SafeHazard/Clip-Boy/Clip-Boy/images/Clip Boy Final - NV 153x192.png

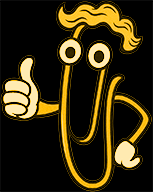
Clip-Boy/images/Clip Boy Final - NV 153x192.png
