SafeHazard/Clip-Boy/Clip-Boy/shots/signal_loss/aplist_01_target_present.bmp

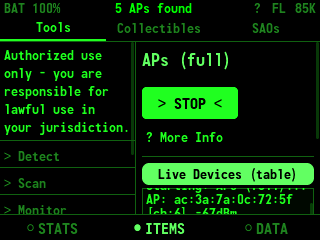
Clip-Boy/shots/signal_loss/aplist_01_target_present.bmp
