SafeHazard/Clip-Boy/Clip-Boy/shots/signal_loss/ble_01_advertiser_up.bmp

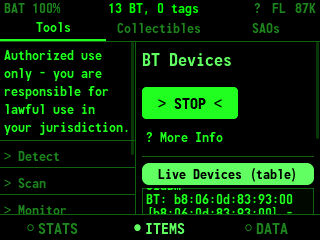
Clip-Boy/shots/signal_loss/ble_01_advertiser_up.bmp
