SafeHazard/Clip-Boy/Clip-Boy/shots/signal_loss/rssi_02_noselect.bmp

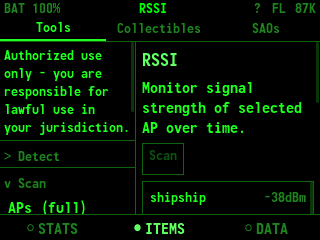
Clip-Boy/shots/signal_loss/rssi_02_noselect.bmp
