SafeHazard/Clip-Boy/Clip-Boy/shots/signal_loss/rssi_03_selected.bmp

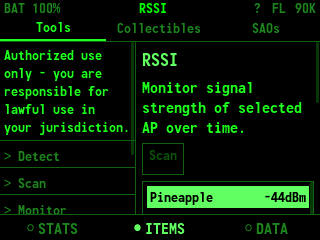
Clip-Boy/shots/signal_loss/rssi_03_selected.bmp
