SafeHazard/Clip-Boy/Clip-Boy/web_images/1.png

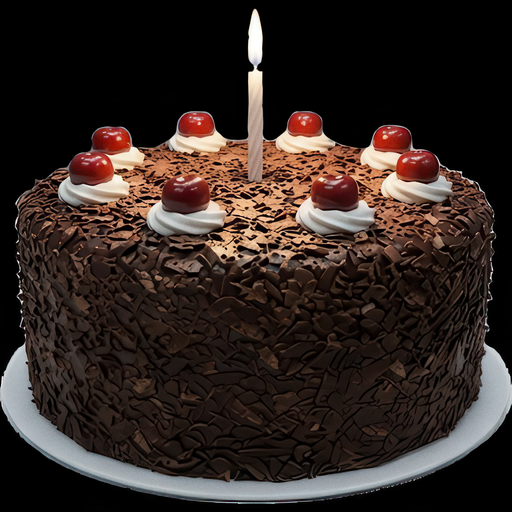
Clip-Boy/web_images/1.png
