SafeHazard/Clip-Boy/Clip-Boy/web_images/2.png

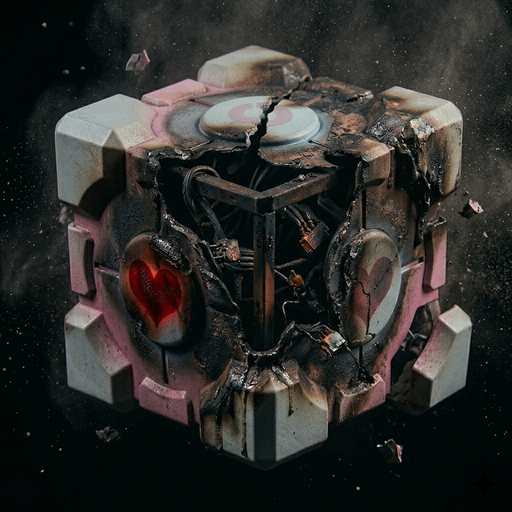
Clip-Boy/web_images/2.png
