SafeHazard/Clip-Boy/Clip-Boy/web_images/3.png

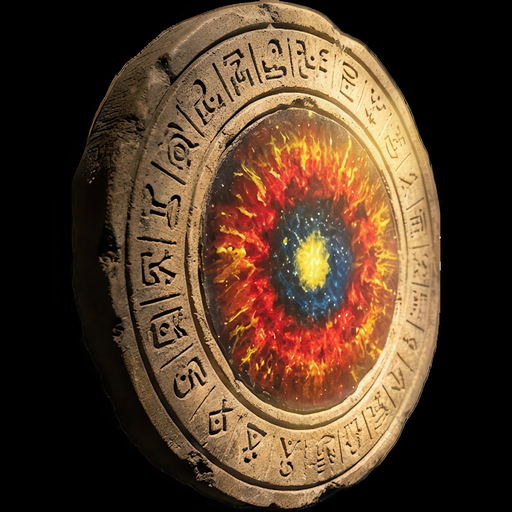
Clip-Boy/web_images/3.png
