SafeHazard/Clip-Boy/Clip-Boy/web_images/4.png

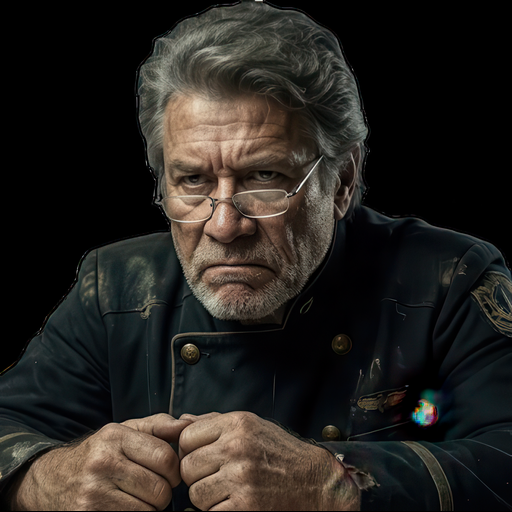
Clip-Boy/web_images/4.png
