SafeHazard/Clip-Boy/Clip-Boy/web_images/5.png

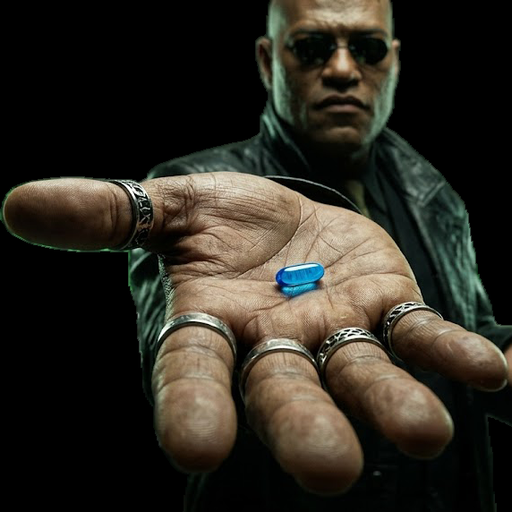
Clip-Boy/web_images/5.png
