SafeHazard/Clip-Boy/Clip-Boy/web_images/6.png

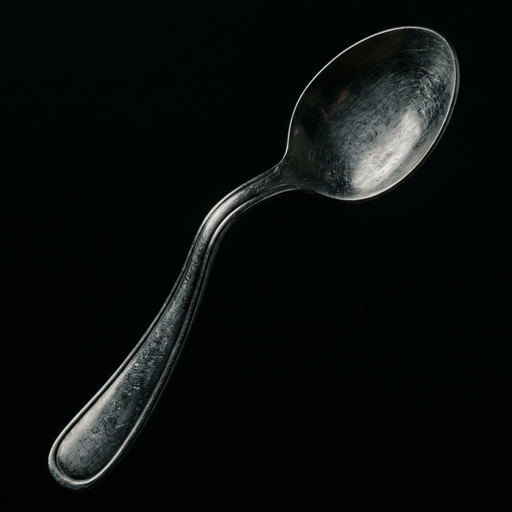
Clip-Boy/web_images/6.png
