SafeHazard/Clip-Boy/Clip-Boy/web_images/7.png

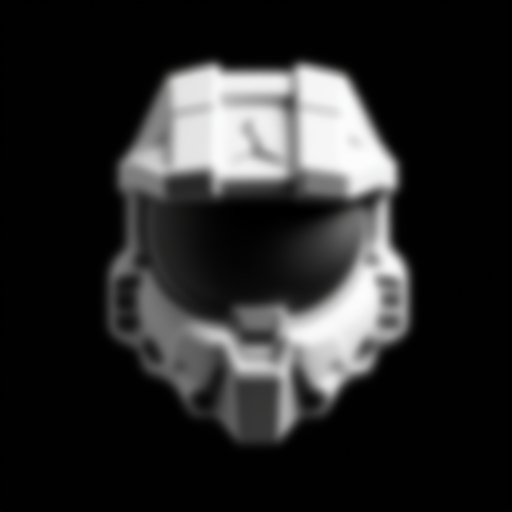
Clip-Boy/web_images/7.png
