SafeHazard/Clip-Boy/Clip-Boy/web_images/8.png

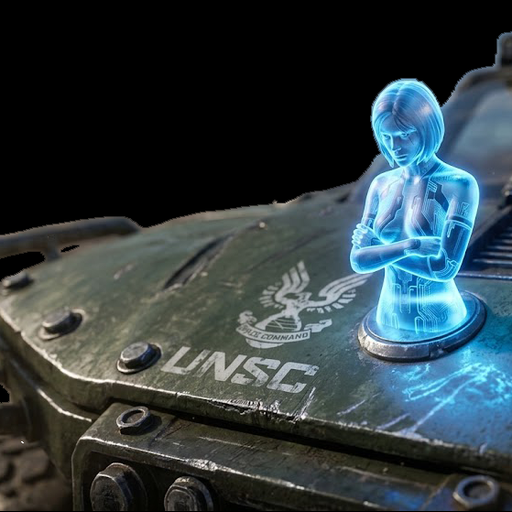
Clip-Boy/web_images/8.png
