SafeHazard/Clip-Boy/Clip-Boy/web_images/9.png

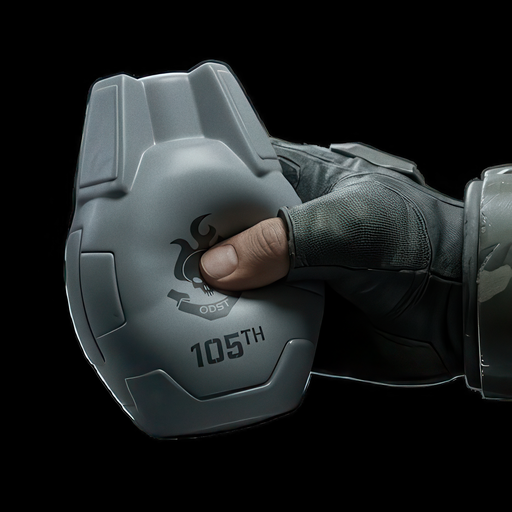
Clip-Boy/web_images/9.png
