SafeHazard/Clip-Boy/Clip-Boy/web_images/10.png

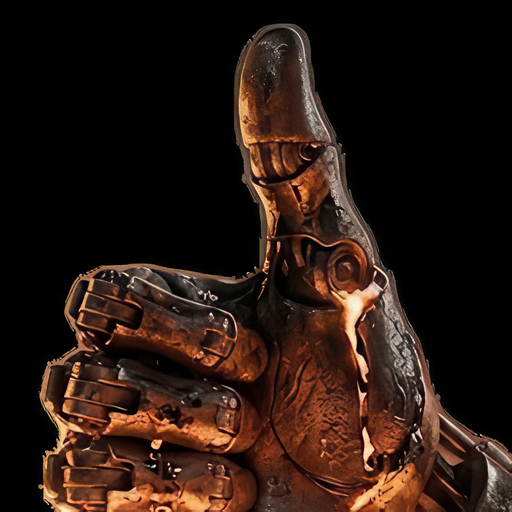
Clip-Boy/web_images/10.png
