SafeHazard/Clip-Boy/Clip-Boy/web_images/12.png

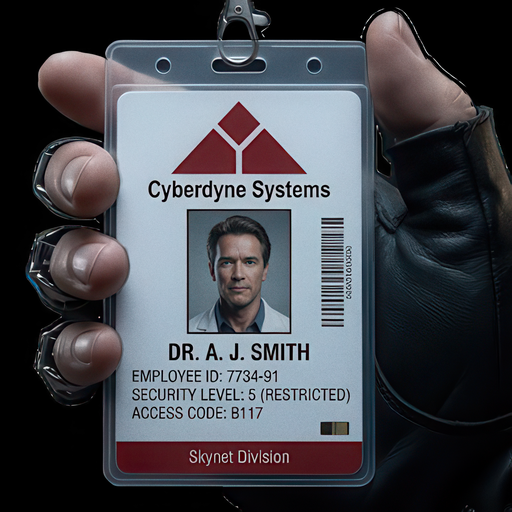
Clip-Boy/web_images/12.png
