SafeHazard/Clip-Boy/Clip-Boy/web_images/13.png

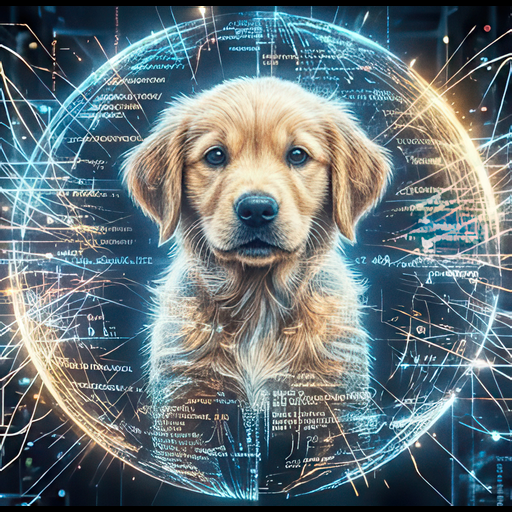
Clip-Boy/web_images/13.png
