SafeHazard/Clip-Boy/Clip-Boy/web_images/14.png

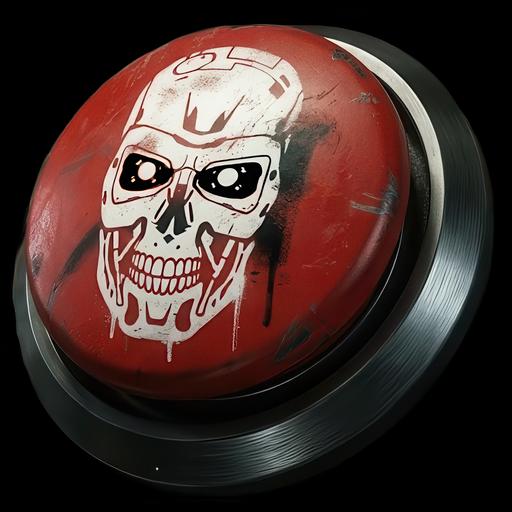
Clip-Boy/web_images/14.png
