SafeHazard/Clip-Boy/Clip-Boy/web_images/15.png

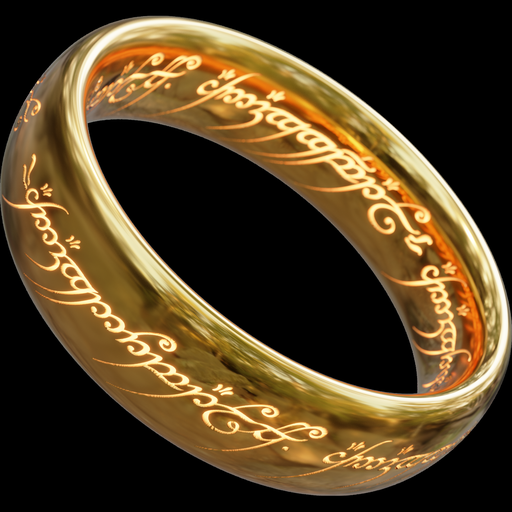
Clip-Boy/web_images/15.png
