SafeHazard/Clip-Boy/Clip-Boy/web_images/16.png

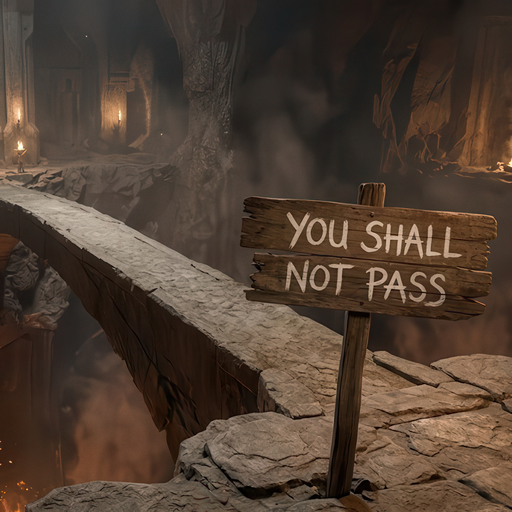
Clip-Boy/web_images/16.png
