SafeHazard/Clip-Boy/Clip-Boy/web_images/17.png

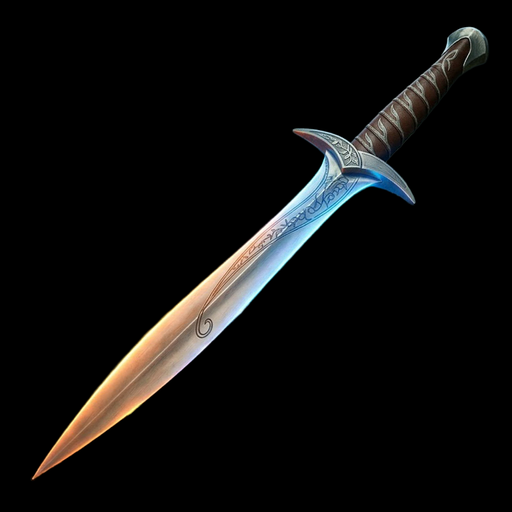
Clip-Boy/web_images/17.png
