SafeHazard/Clip-Boy/Clip-Boy/web_images/18.png

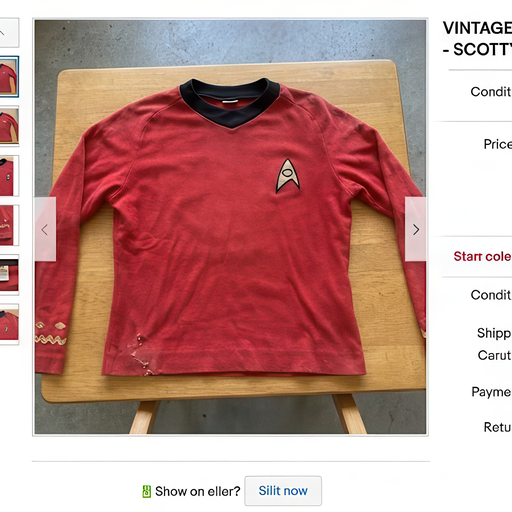
Clip-Boy/web_images/18.png
