SafeHazard/Clip-Boy/Clip-Boy/web_images/19.png

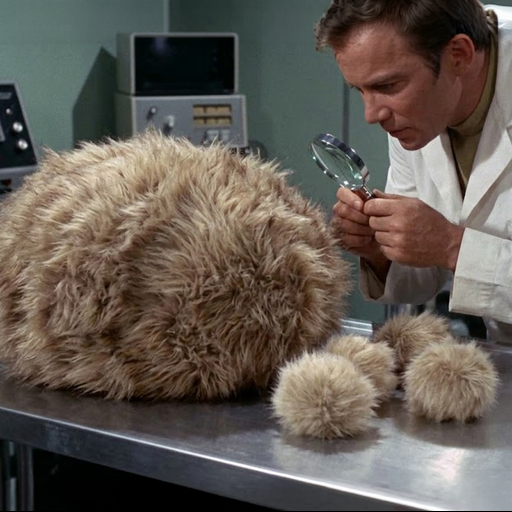
Clip-Boy/web_images/19.png
