SafeHazard/Clip-Boy/Clip-Boy/web_images/20.png

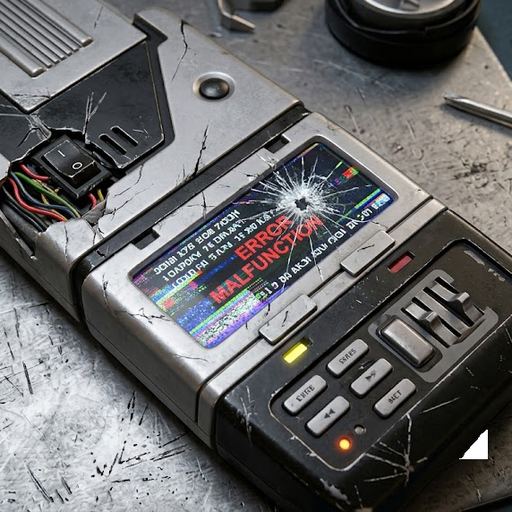
Clip-Boy/web_images/20.png
