SafeHazard/Clip-Boy/Clip-Boy/web_images/21.png

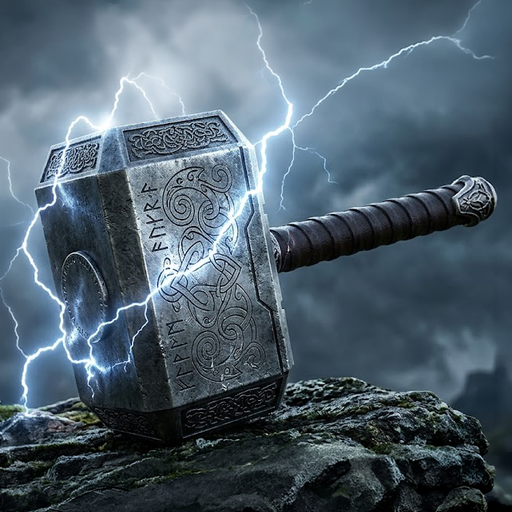
Clip-Boy/web_images/21.png
