SafeHazard/Clip-Boy/Clip-Boy/web_images/22.png

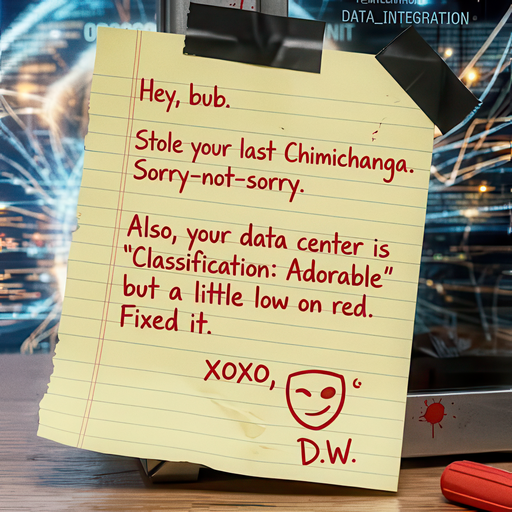
Clip-Boy/web_images/22.png
