SafeHazard/Clip-Boy/Clip-Boy/web_images/23.png

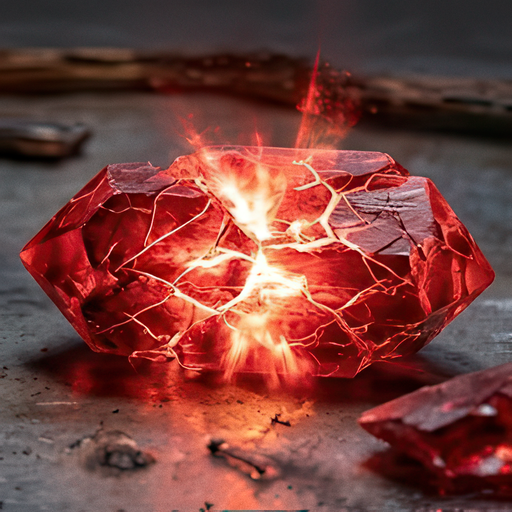
Clip-Boy/web_images/23.png
