SafeHazard/Clip-Boy/Clip-Boy/web_images/26.png

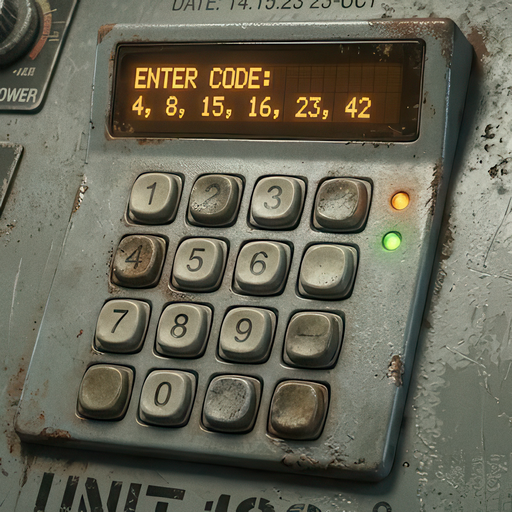
Clip-Boy/web_images/26.png
