SafeHazard/Clip-Boy/Clip-Boy/web_images/27.png

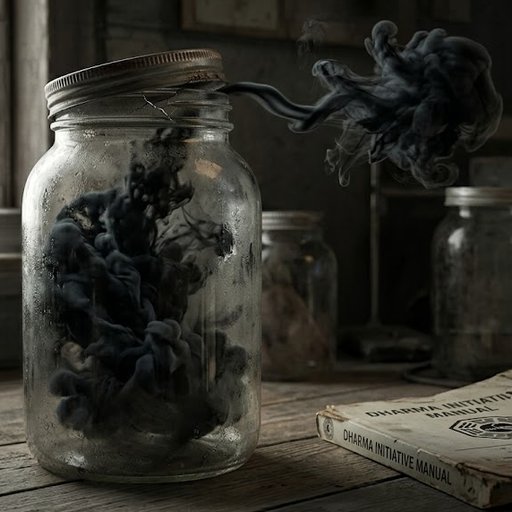
Clip-Boy/web_images/27.png
