SafeHazard/Clip-Boy/Clip-Boy/web_images/28.png

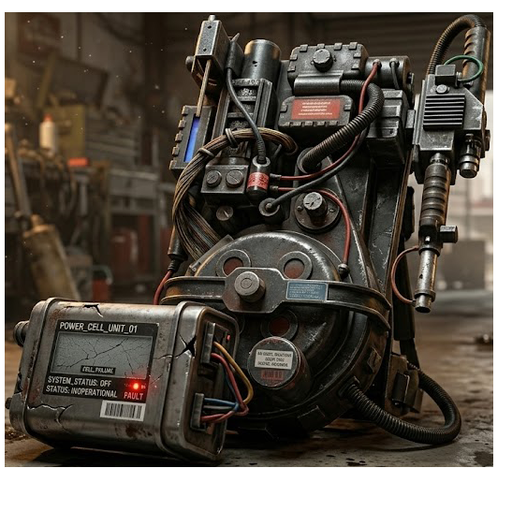
Clip-Boy/web_images/28.png
