SafeHazard/Clip-Boy/Clip-Boy/web_images/29.png

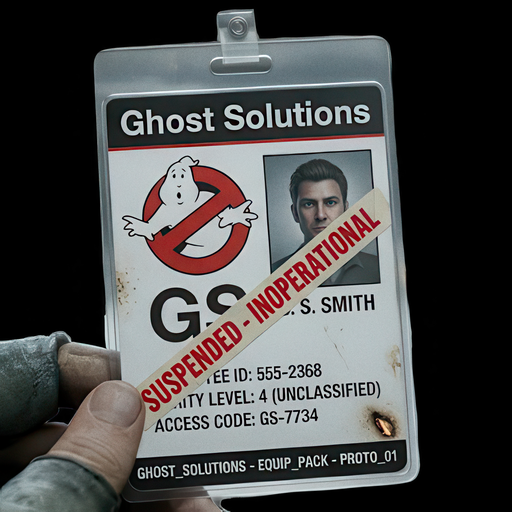
Clip-Boy/web_images/29.png
