SafeHazard/Clip-Boy/Clip-Boy/web_images/30.png

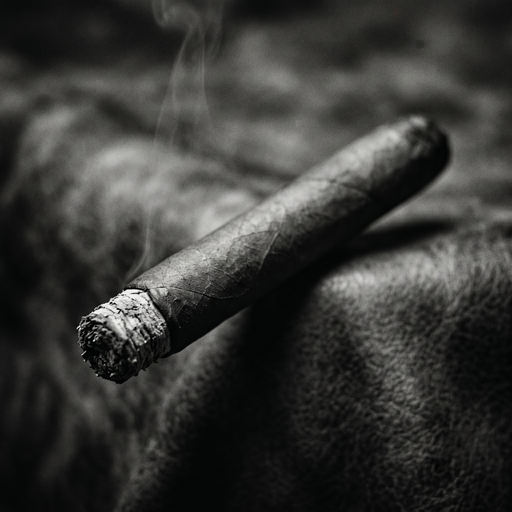
Clip-Boy/web_images/30.png
