SafeHazard/Clip-Boy/Clip-Boy/web_images/31.png

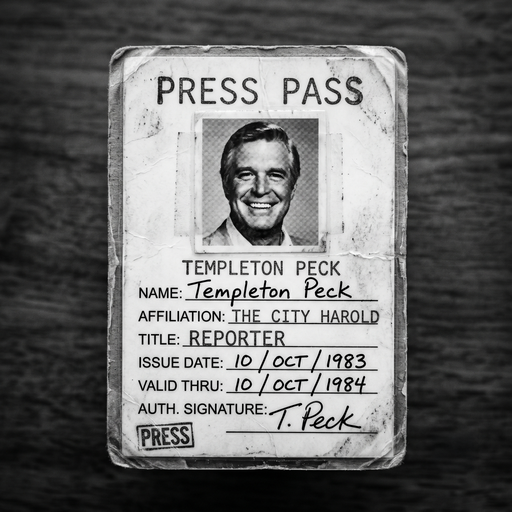
Clip-Boy/web_images/31.png
