SafeHazard/Clip-Boy/Clip-Boy/web_images/32.png

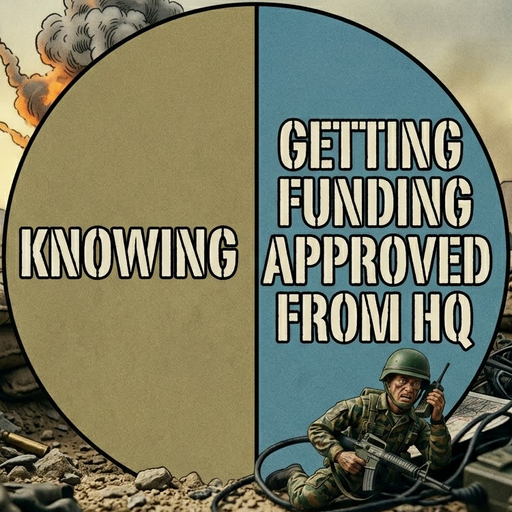
Clip-Boy/web_images/32.png
