SafeHazard/Clip-Boy/Clip-Boy/web_images/33.png

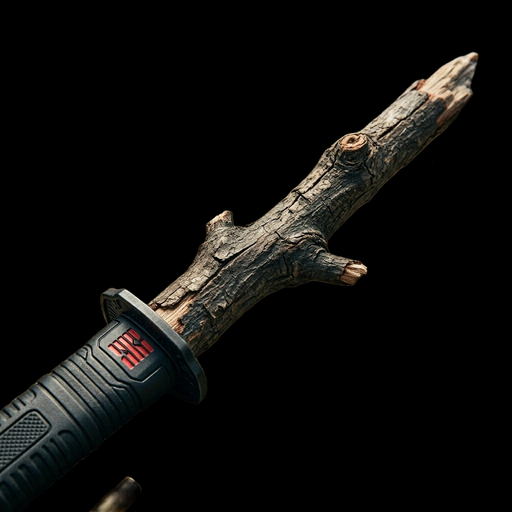
Clip-Boy/web_images/33.png
