SafeHazard/Clip-Boy/Clip-Boy/web_images/34.png

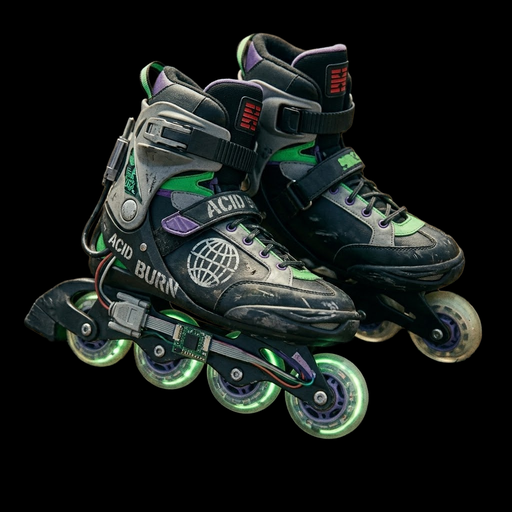
Clip-Boy/web_images/34.png
