SafeHazard/Clip-Boy/Clip-Boy/web_images/35.png

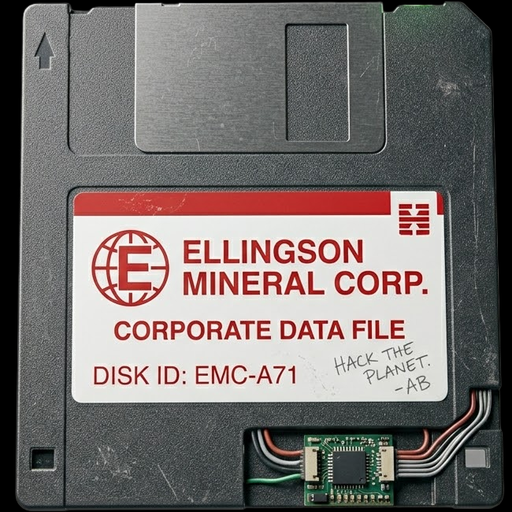
Clip-Boy/web_images/35.png
