SafeHazard/Clip-Boy/Clip-Boy/web_images/36.png

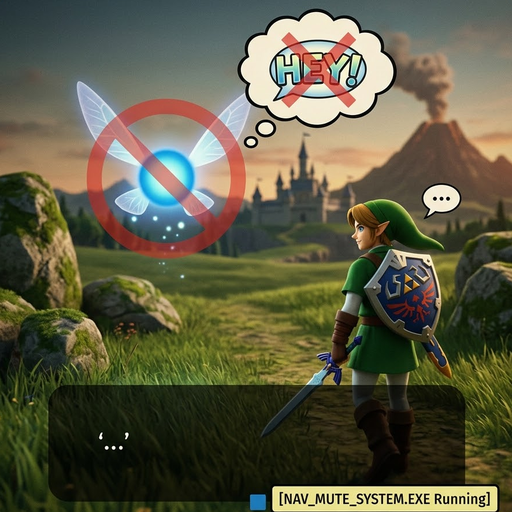
Clip-Boy/web_images/36.png
