SafeHazard/Clip-Boy/Clip-Boy/web_images/37.png

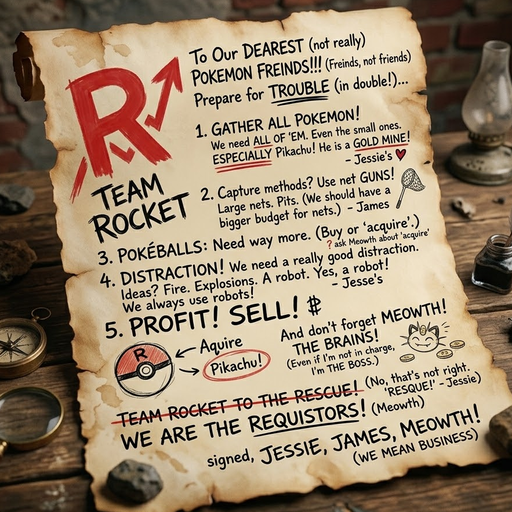
Clip-Boy/web_images/37.png
