SafeHazard/Clip-Boy/Clip-Boy/web_images/38.png

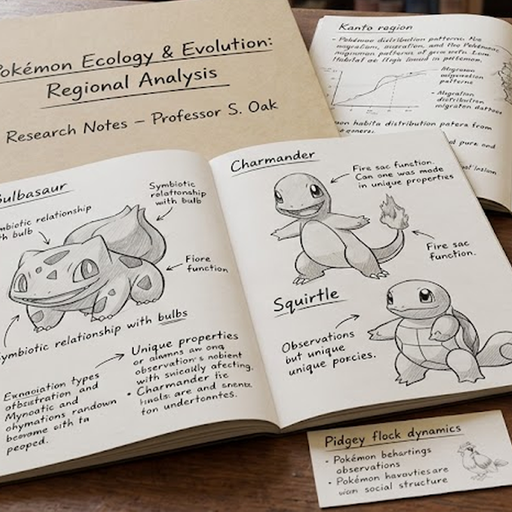
Clip-Boy/web_images/38.png
