SafeHazard/Clip-Boy/Clip-Boy/web_images/39.png

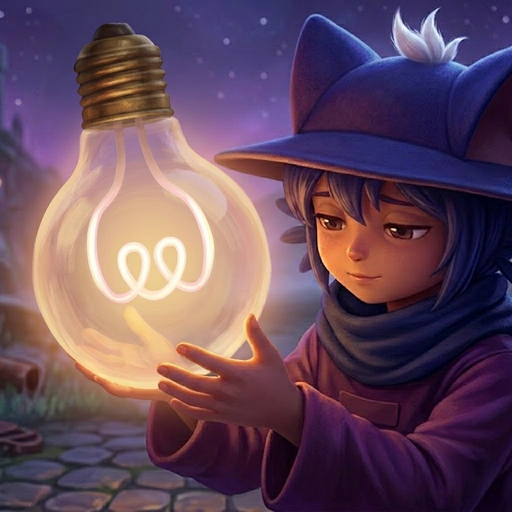
Clip-Boy/web_images/39.png
