SafeHazard/Clip-Boy/Clip-Boy/web_images/42.png

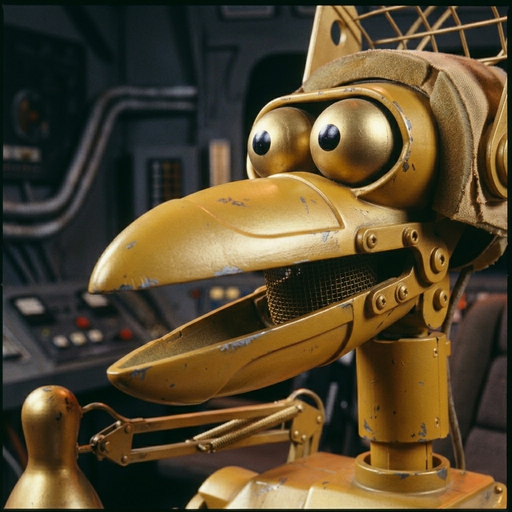
Clip-Boy/web_images/42.png
