SafeHazard/Clip-Boy/Clip-Boy/web_images/44.png

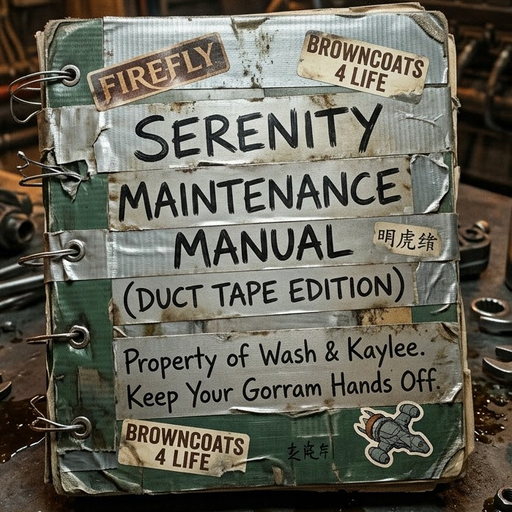
Clip-Boy/web_images/44.png
