SafeHazard/Clip-Boy/Clip-Boy/web_images/45.png

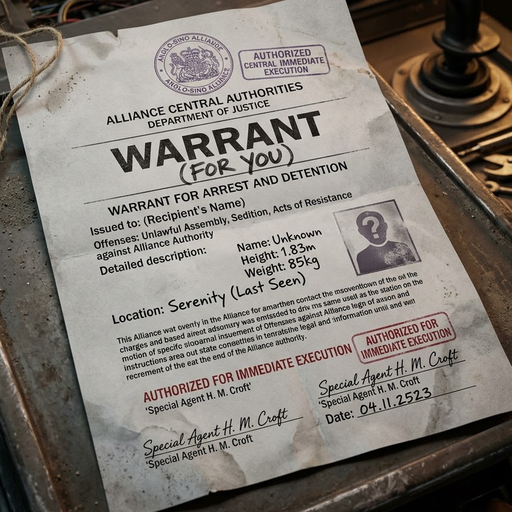
Clip-Boy/web_images/45.png
