SafeHazard/Clip-Boy/Clip-Boy/web_images/46.png

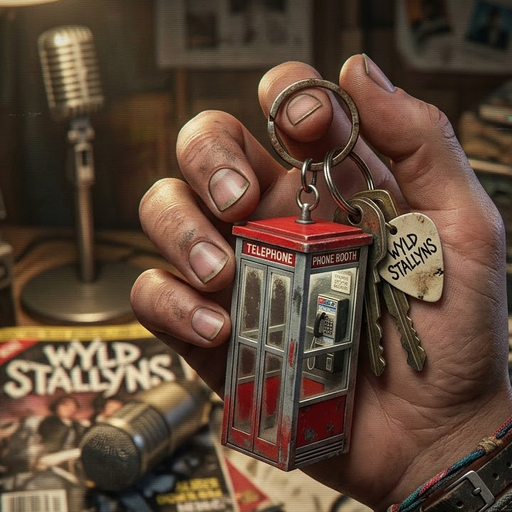
Clip-Boy/web_images/46.png
