SafeHazard/Clip-Boy/Clip-Boy/web_images/47.png

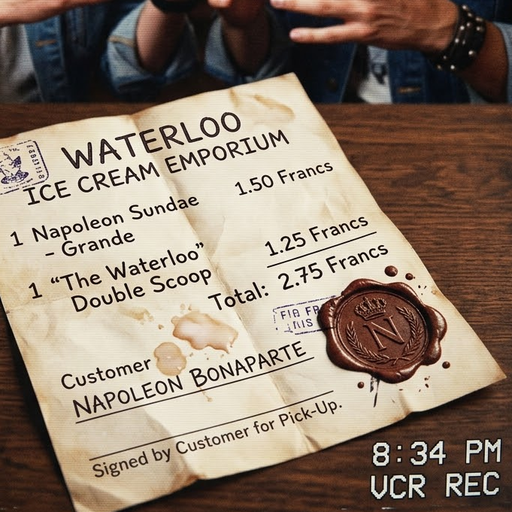
Clip-Boy/web_images/47.png
