SafeHazard/Clip-Boy/Clip-Boy/web_images/48.png

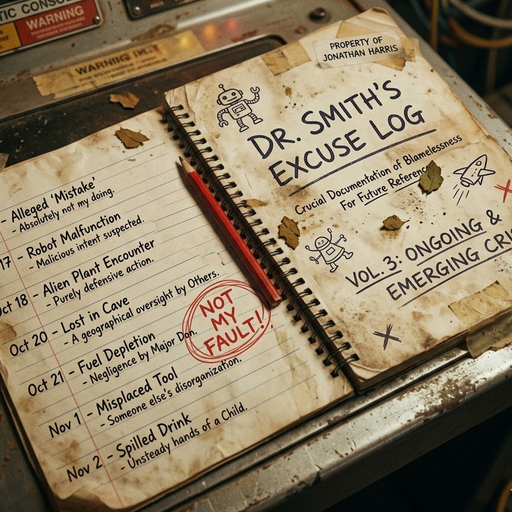
Clip-Boy/web_images/48.png
