SafeHazard/Clip-Boy/Clip-Boy/web_images/49.png

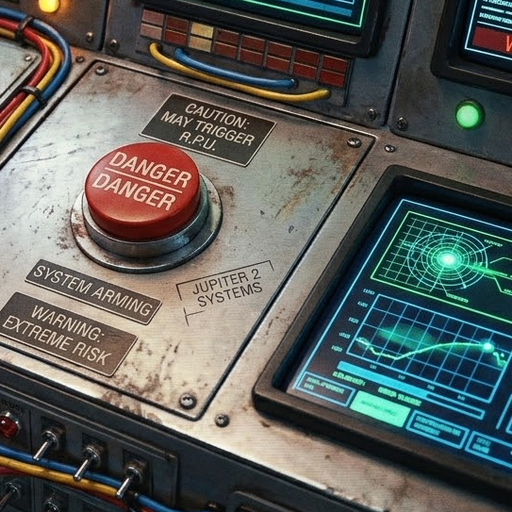
Clip-Boy/web_images/49.png
