SafeHazard/Clip-Boy/Clip-Boy/web_images/50.png

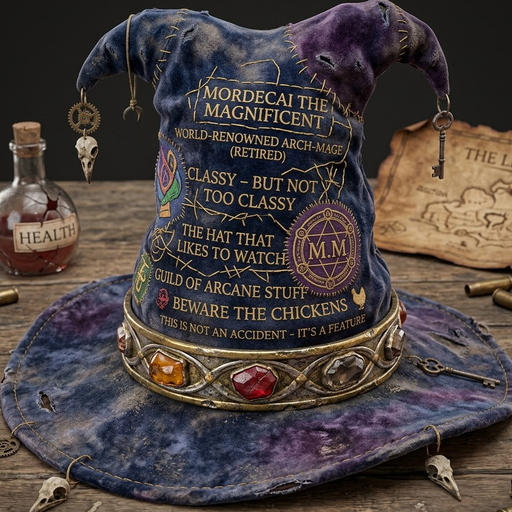
Clip-Boy/web_images/50.png
