SafeHazard/Clip-Boy/Clip-Boy/web_images/51.png

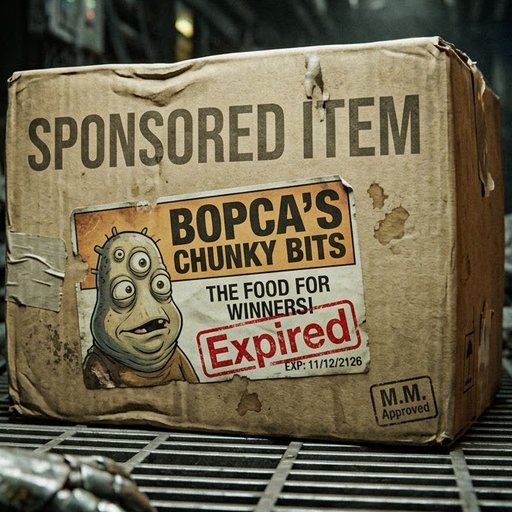
Clip-Boy/web_images/51.png
