SafeHazard/Clip-Boy/Clip-Boy/web_images/52.png

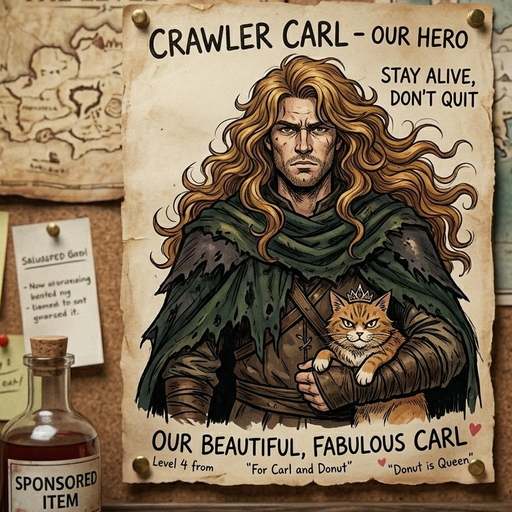
Clip-Boy/web_images/52.png
