SafeHazard/Clip-Boy/Clip-Boy/web_images/53.png

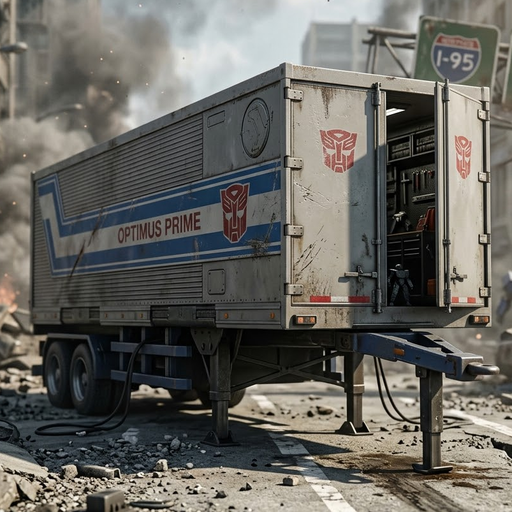
Clip-Boy/web_images/53.png
