SafeHazard/Clip-Boy/Clip-Boy/web_images/54.png

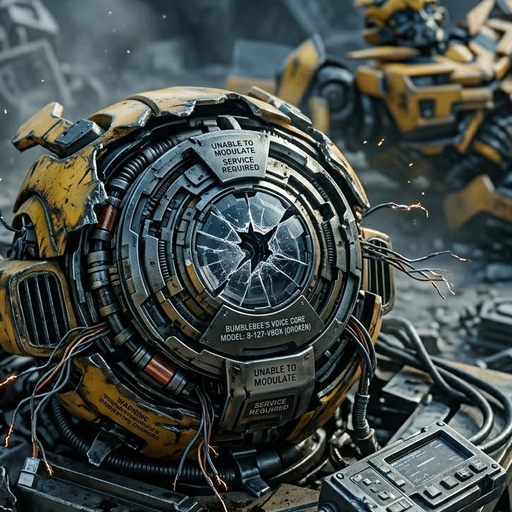
Clip-Boy/web_images/54.png
