SafeHazard/Clip-Boy/Clip-Boy/web_images/55.png

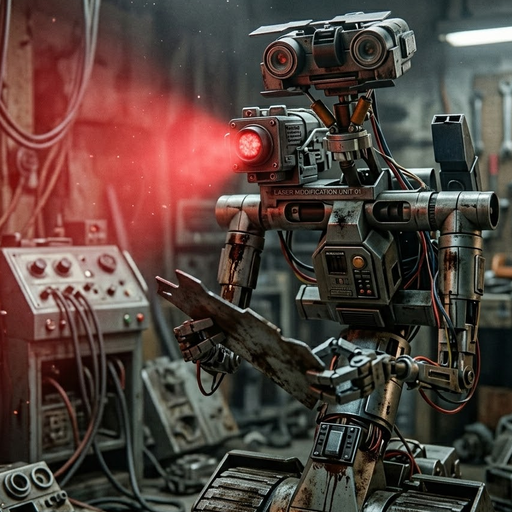
Clip-Boy/web_images/55.png
