SafeHazard/Clip-Boy/Clip-Boy/web_images/56.png

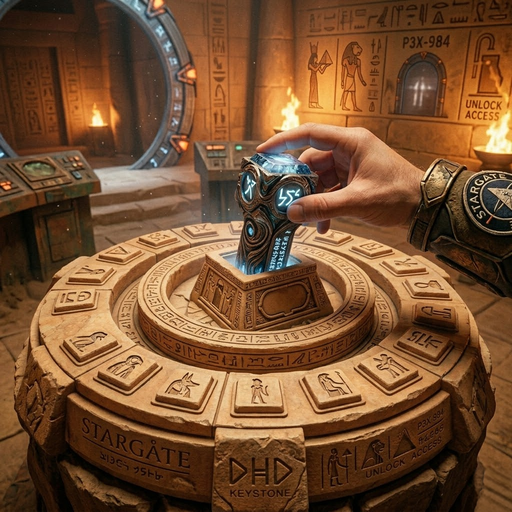
Clip-Boy/web_images/56.png
