SafeHazard/Clip-Boy/Clip-Boy/web_images/57.png

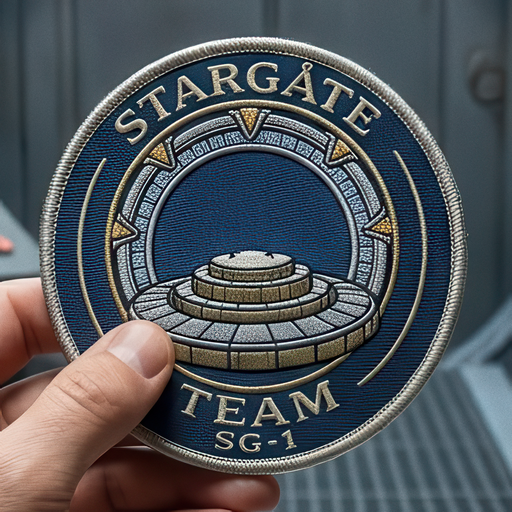
Clip-Boy/web_images/57.png
