SafeHazard/Clip-Boy/Clip-Boy/web_images/58.png

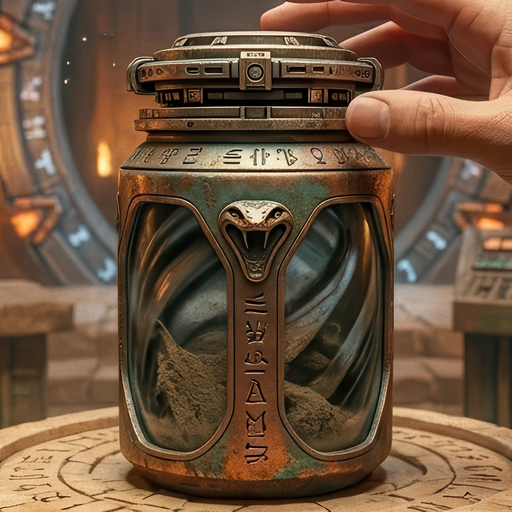
Clip-Boy/web_images/58.png
