SafeHazard/Clip-Boy/Clip-Boy/web_images/60.png

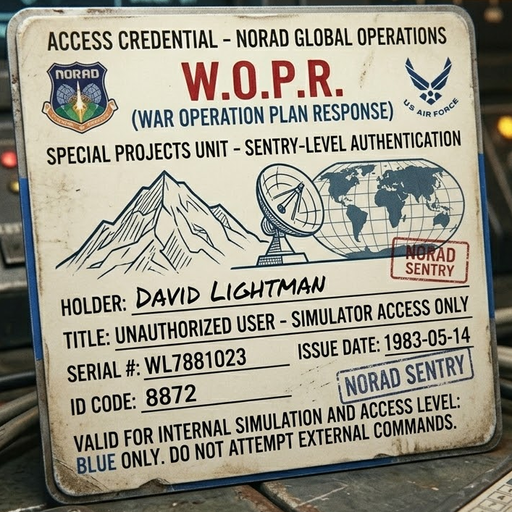
Clip-Boy/web_images/60.png
