SafeHazard/Clip-Boy/Clip-Boy/web_images/61.png

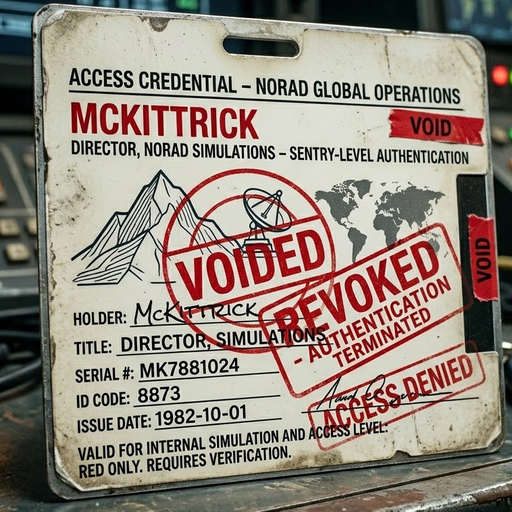
Clip-Boy/web_images/61.png
