SafeHazard/Clip-Boy/Clip-Boy/web_images/62.png

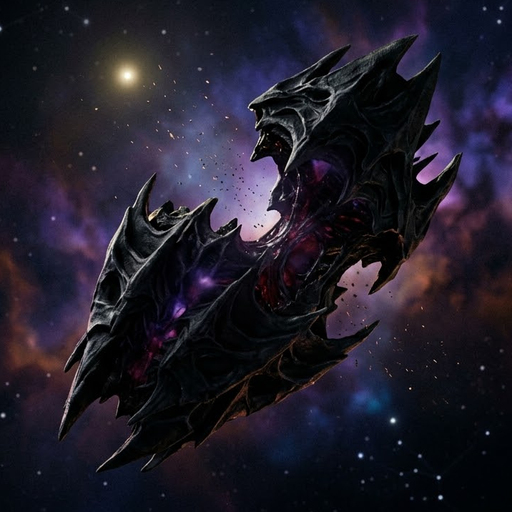
Clip-Boy/web_images/62.png
