SafeHazard/Clip-Boy/Clip-Boy/web_images/63.png

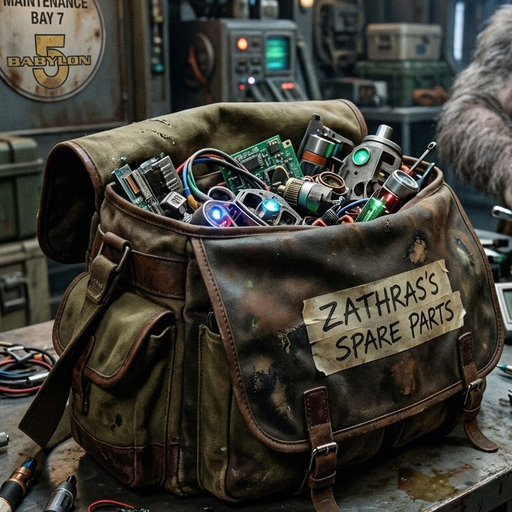
Clip-Boy/web_images/63.png
