SafeHazard/Clip-Boy/Clip-Boy/web_images/64.png

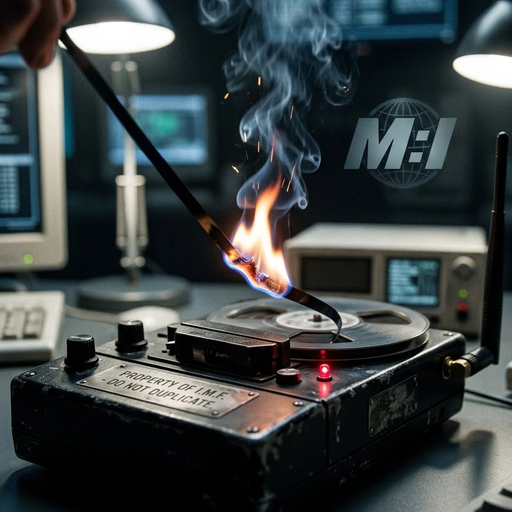
Clip-Boy/web_images/64.png
