SafeHazard/Clip-Boy/Clip-Boy/web_images/66.png

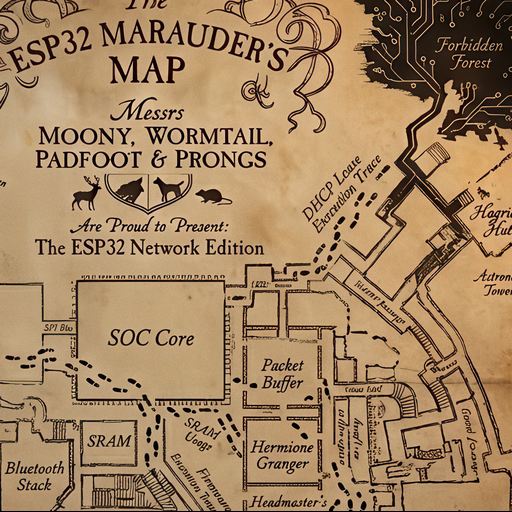
Clip-Boy/web_images/66.png
