SafeHazard/Clip-Boy/Clip-Boy/web_images/67.png

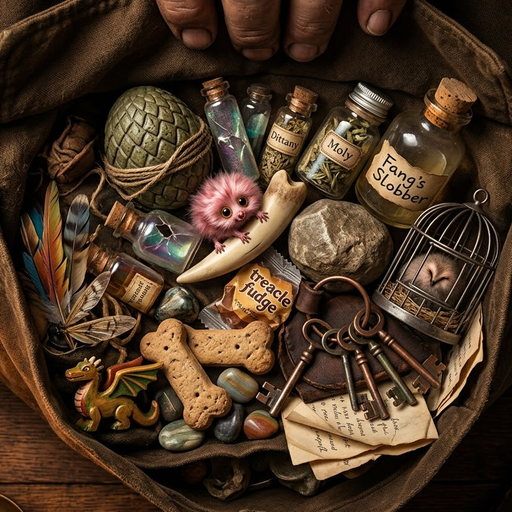
Clip-Boy/web_images/67.png
