SafeHazard/Clip-Boy/Clip-Boy/web_images/68.png

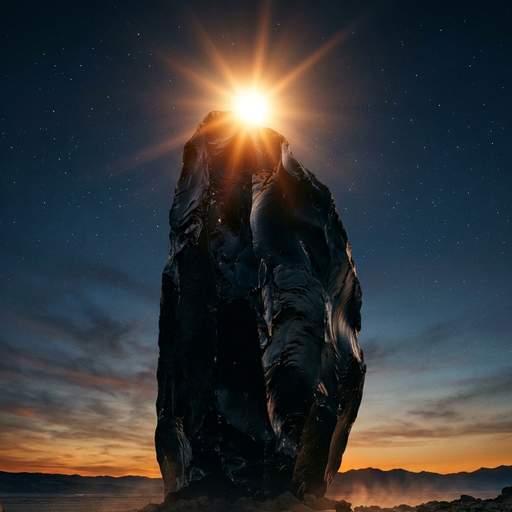
Clip-Boy/web_images/68.png
