SafeHazard/Clip-Boy/Clip-Boy/web_images/69.png

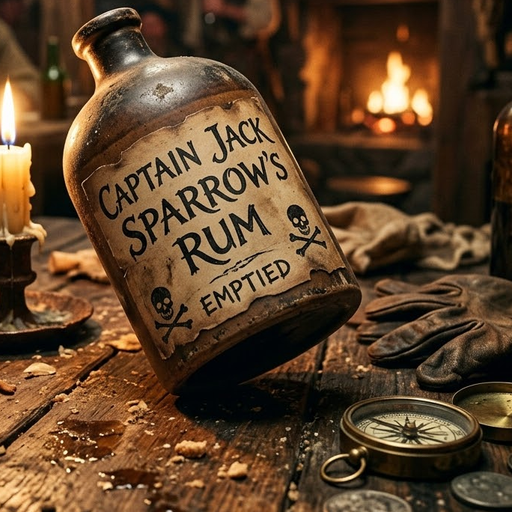
Clip-Boy/web_images/69.png
