SafeHazard/Clip-Boy/Clip-Boy/web_images/70.png

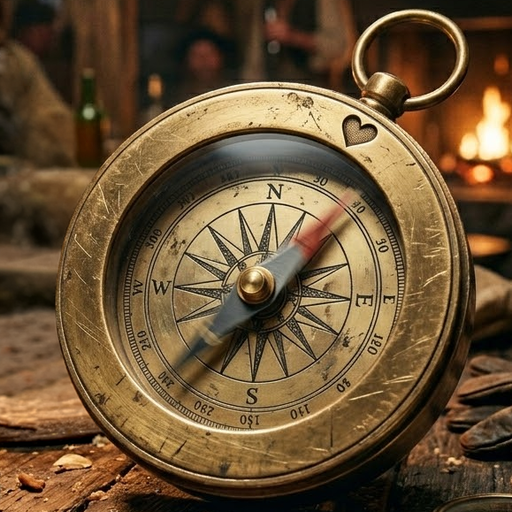
Clip-Boy/web_images/70.png
