SafeHazard/Clip-Boy/Clip-Boy/web_images/71.png

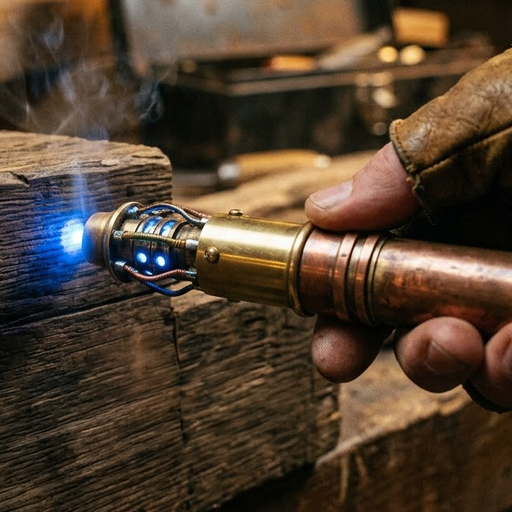
Clip-Boy/web_images/71.png
