SafeHazard/Clip-Boy/Clip-Boy/web_images/72.png

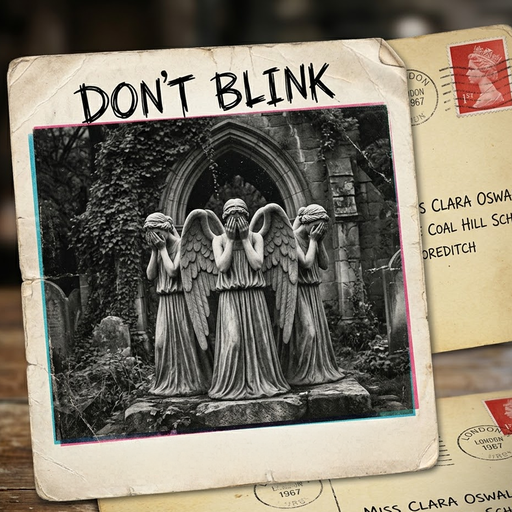
Clip-Boy/web_images/72.png
