SafeHazard/Clip-Boy/Clip-Boy/web_images/73.png

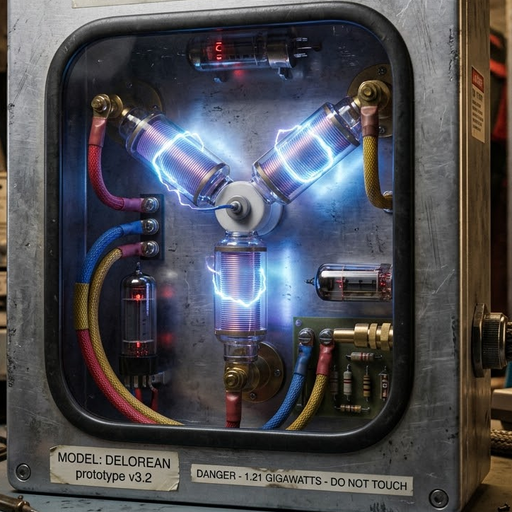
Clip-Boy/web_images/73.png
