SafeHazard/Clip-Boy/Clip-Boy/web_images/74.png

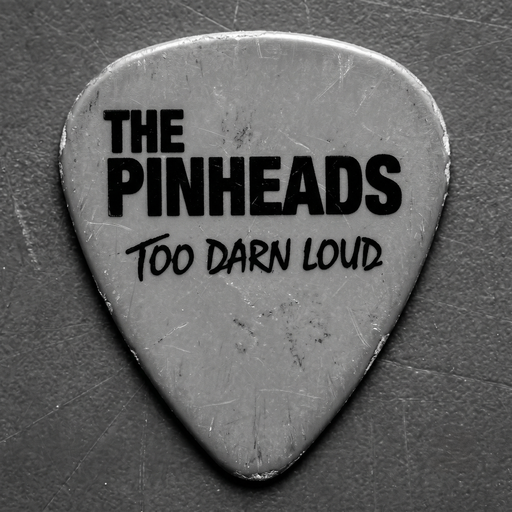
Clip-Boy/web_images/74.png
