SafeHazard/Clip-Boy/Clip-Boy/web_images/75.png

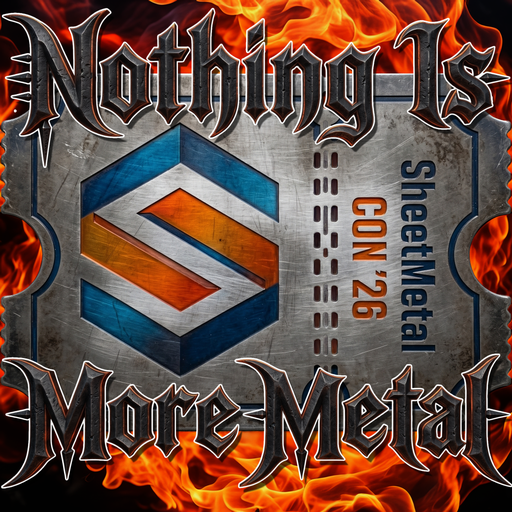
Clip-Boy/web_images/75.png
