SafeHazard/Clip-Boy/Clip-Boy/web_images/76.png

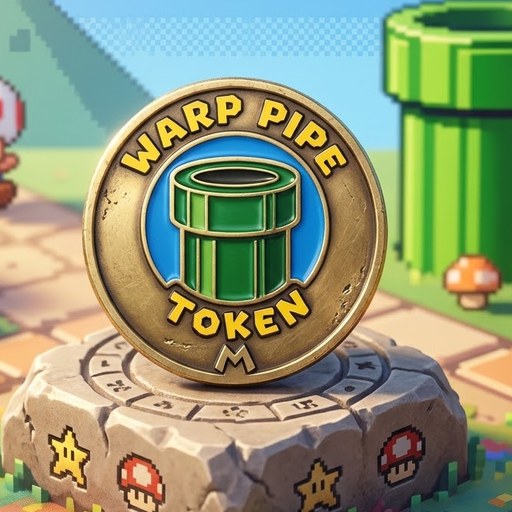
Clip-Boy/web_images/76.png
