SafeHazard/Clip-Boy/Clip-Boy/web_images/77.png

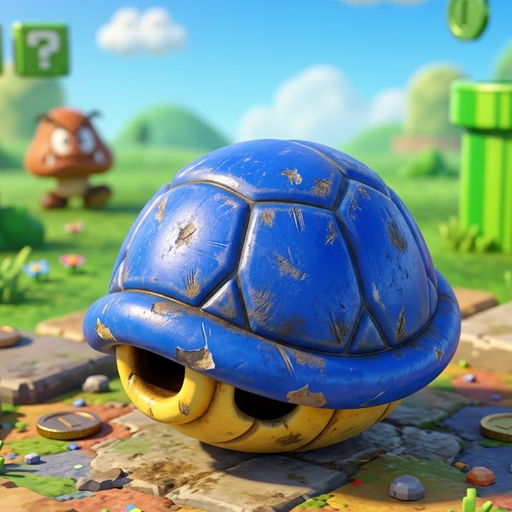
Clip-Boy/web_images/77.png
