SafeHazard/Clip-Boy/Clip-Boy/web_images/78.png

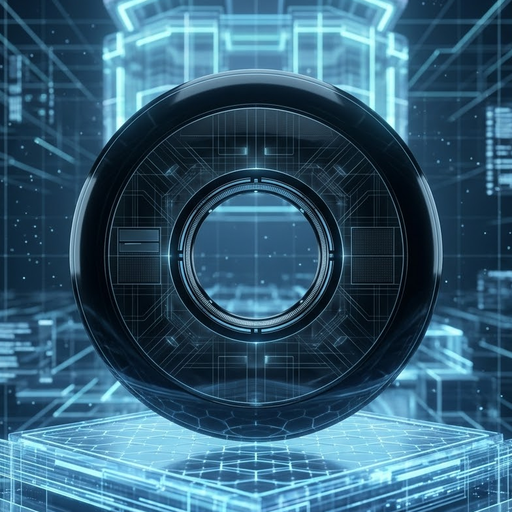
Clip-Boy/web_images/78.png
