SafeHazard/Clip-Boy/Clip-Boy/web_images/79.png

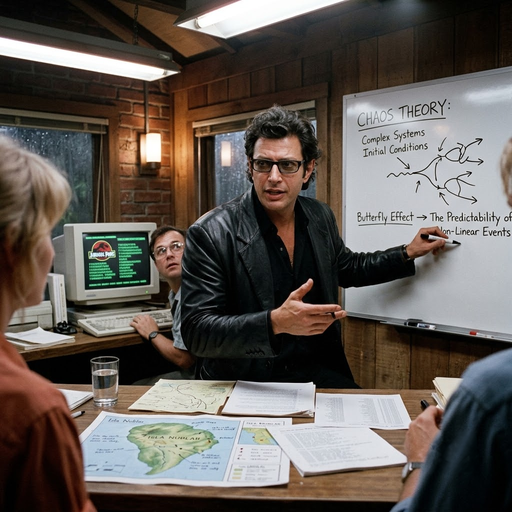
Clip-Boy/web_images/79.png
