SafeHazard/Clip-Boy/Clip-Boy/web_images/80.png

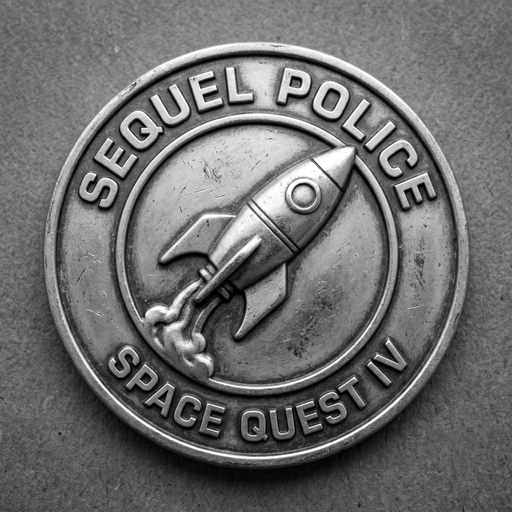
Clip-Boy/web_images/80.png
