SafeHazard/Clip-Boy/Clip-Boy/web_images/81.png

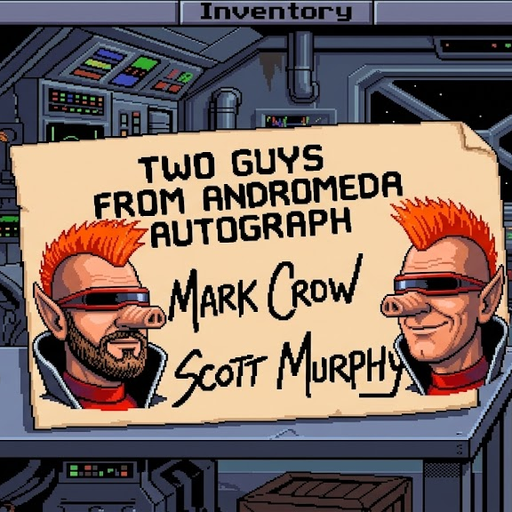
Clip-Boy/web_images/81.png
