SafeHazard/Clip-Boy/Clip-Boy/web_images/82.png

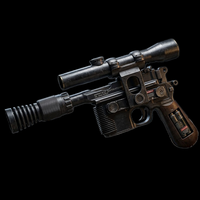
Clip-Boy/web_images/82.png
