SafeHazard/Clip-Boy/Clip-Boy/web_images/83.png

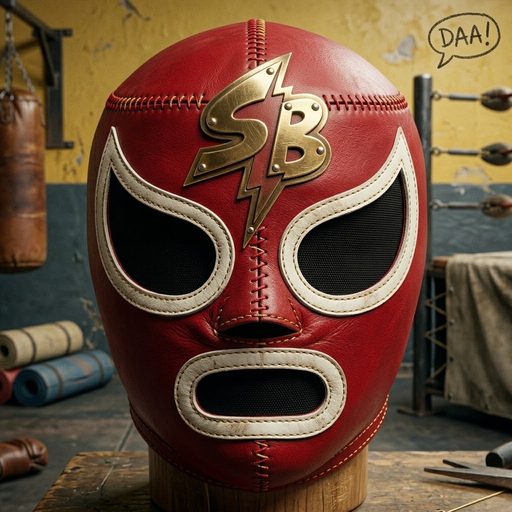
Clip-Boy/web_images/83.png
