SafeHazard/Clip-Boy/Clip-Boy/web_images/84.png

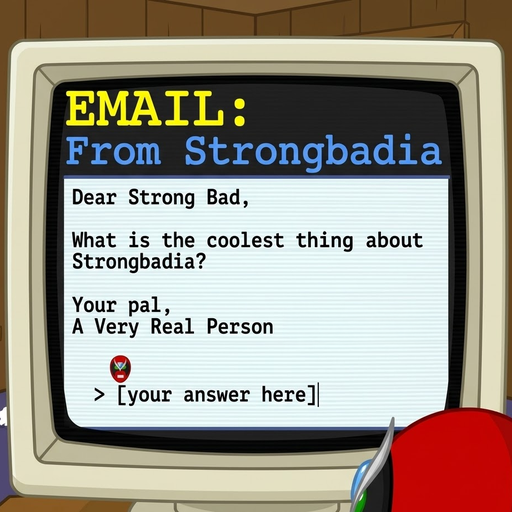
Clip-Boy/web_images/84.png
