SafeHazard/Clip-Boy/Clip-Boy/web_images/85.png

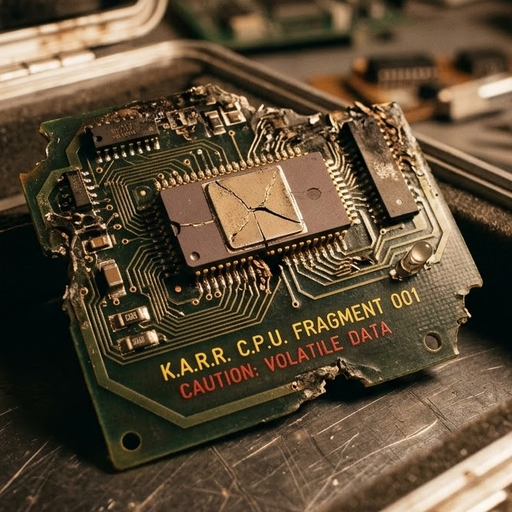
Clip-Boy/web_images/85.png
