SafeHazard/Clip-Boy/Clip-Boy/web_images/86.png

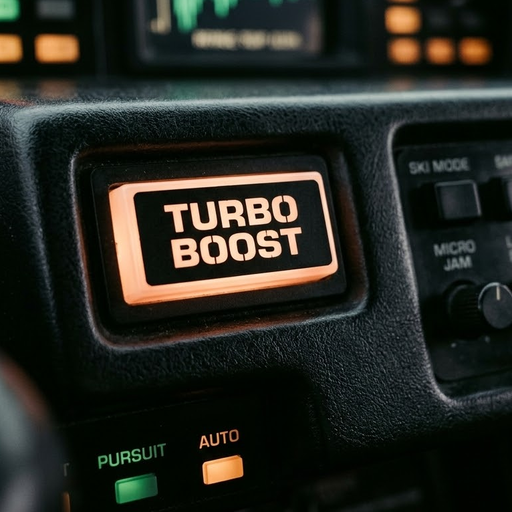
Clip-Boy/web_images/86.png
