SafeHazard/Clip-Boy/Clip-Boy/web_images/87.png

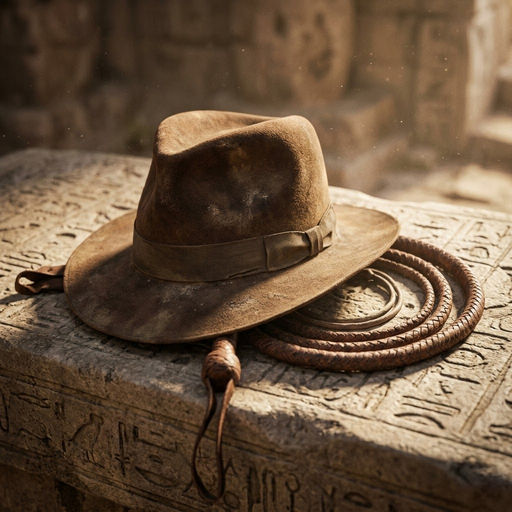
Clip-Boy/web_images/87.png
