SafeHazard/Clip-Boy/Clip-Boy/web_images/88.png

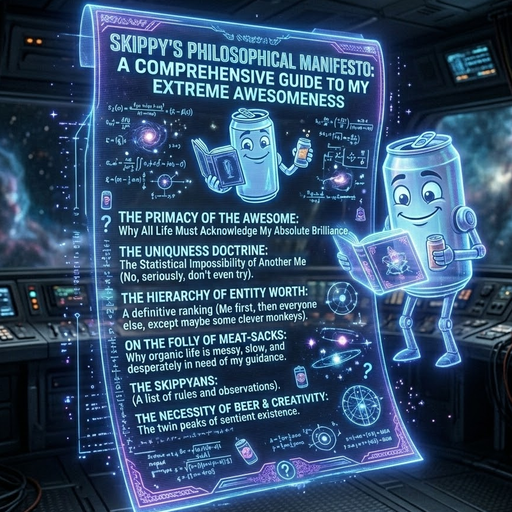
Clip-Boy/web_images/88.png
