SafeHazard/Clip-Boy/Clip-Boy/web_images/89.png

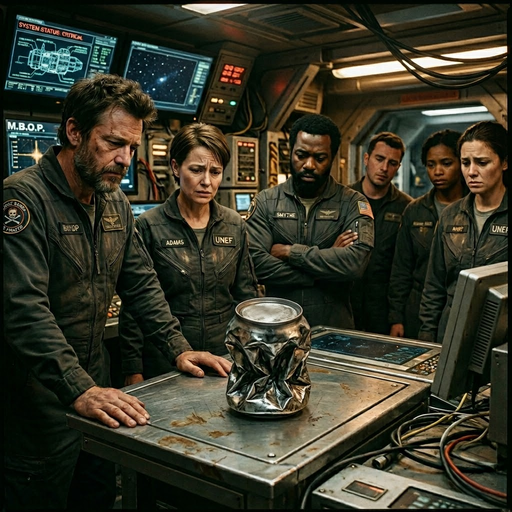
Clip-Boy/web_images/89.png
