SafeHazard/Clip-Boy/Clip-Boy/web_images/90.png

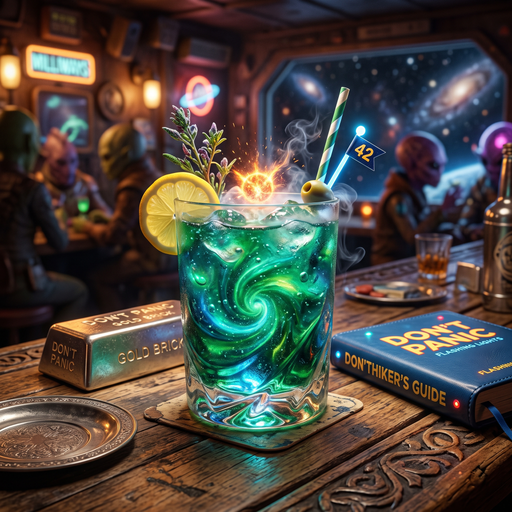
Clip-Boy/web_images/90.png
