SafeHazard/Clip-Boy/Clip-Boy/web_images/92.png

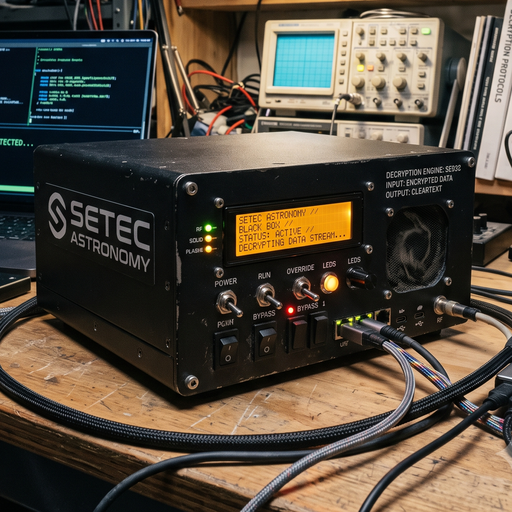
Clip-Boy/web_images/92.png
