SafeHazard/Clip-Boy/Clip-Boy/web_images/93.png

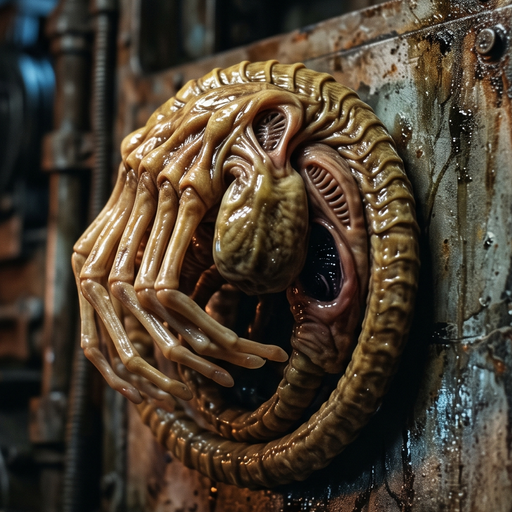
Clip-Boy/web_images/93.png
