SafeHazard/Clip-Boy/Clip-Boy/web_images/95.png

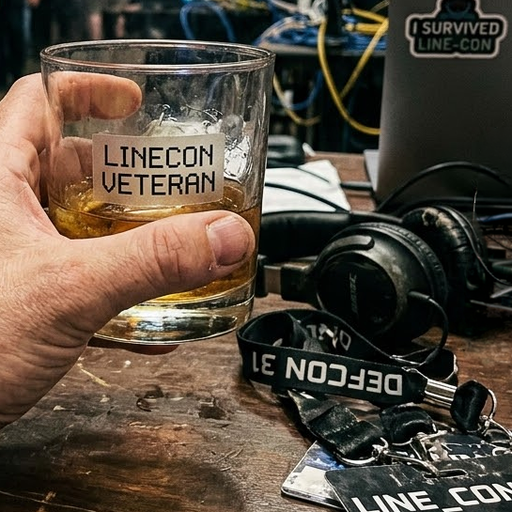
Clip-Boy/web_images/95.png
