SafeHazard/Clip-Boy/Clip-Boy/web_images/96.png

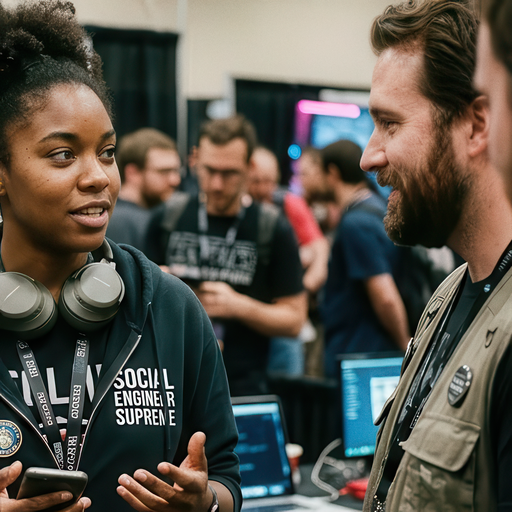
Clip-Boy/web_images/96.png
