SafeHazard/Clip-Boy/Clip-Boy/web_images/97.png

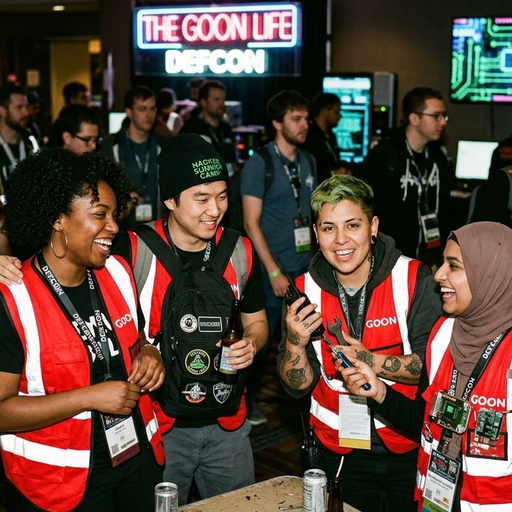
Clip-Boy/web_images/97.png
