SafeHazard/Clip-Boy/Clip-Boy/web_images/98.png

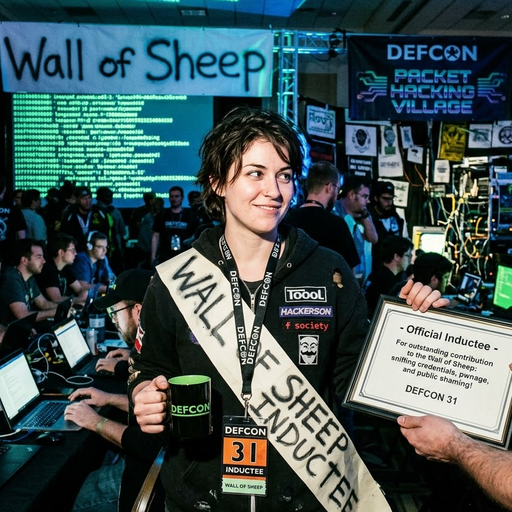
Clip-Boy/web_images/98.png
