SafeHazard/Clip-Boy/Clip-Boy/web_images/99.png

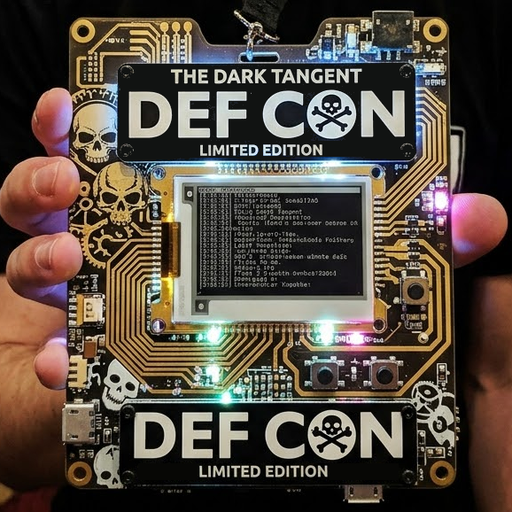
Clip-Boy/web_images/99.png
