SafeHazard/Clip-Boy/Clip-Boy/web_images/100.png

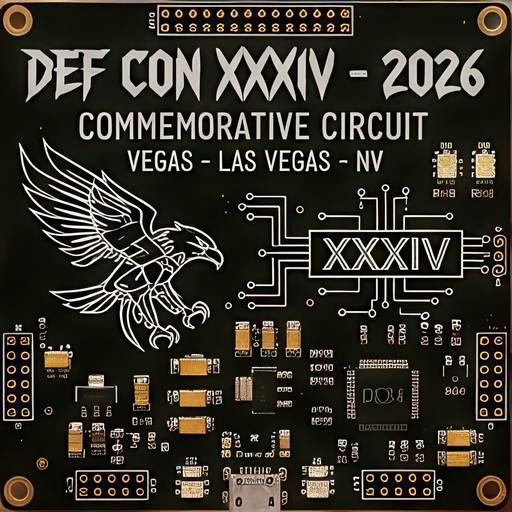
Clip-Boy/web_images/100.png
