SafeHazard/Clip-Boy/Clip-Boy/web_images/108.png

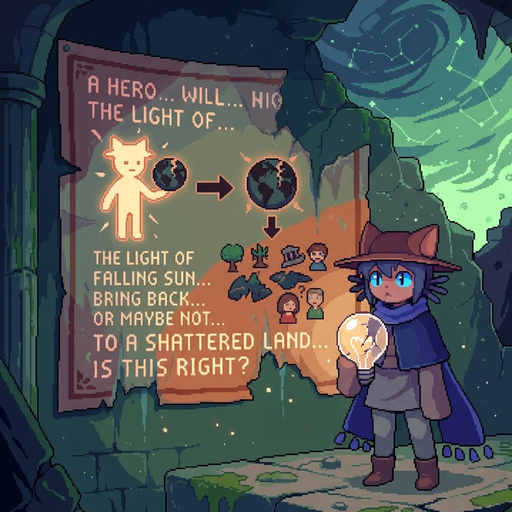
Clip-Boy/web_images/108.png
