SafeHazard/Clip-Boy/Clip-Boy/web_images/112.png

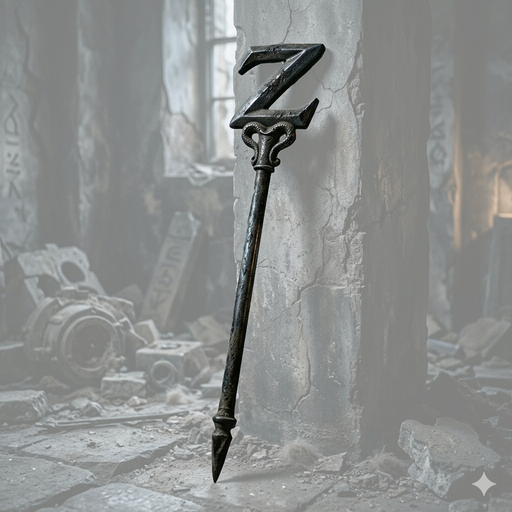
Clip-Boy/web_images/112.png
