SafeHazard/Clip-Boy/Clip-Boy/web_images/118.png

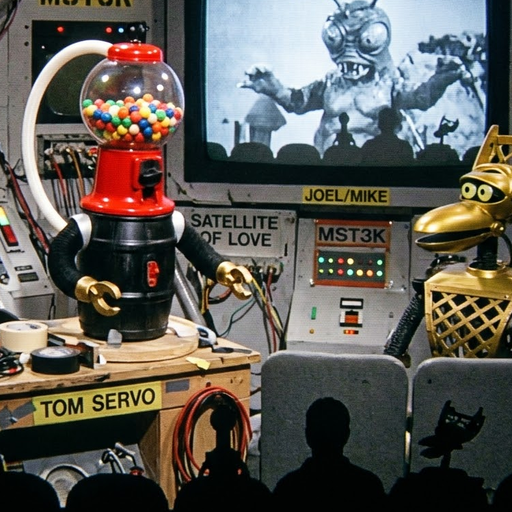
Clip-Boy/web_images/118.png
