SafeHazard/Clip-Boy/Clip-Boy/web_images/127.png

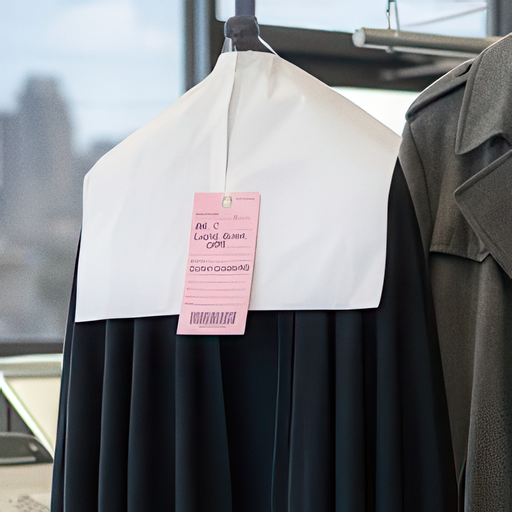
Clip-Boy/web_images/127.png
