SafeHazard/Clip-Boy/Clip-Boy/tags/38.3mf

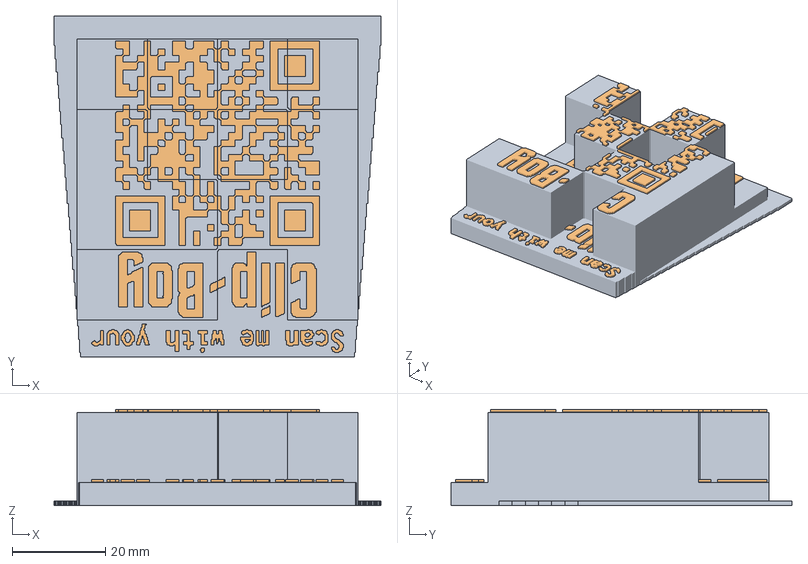
[picture p111: CAD file, 2026-08-05]
Clip-Boy/tags/38.3mf
70.0 x 73.0 x 20.6 mm
HM_white
HM_black_cap
