SafeHazard/Clip-Boy/Clip-Boy/BAT_Driver.cpp

#include "BAT_Driver.h"
#include "esp_adc_cal.h"

#define BAT_ADC_PIN 8
#define DEFAULT_VREF 1100  // ESP32 default reference voltage in mV
#define MEASUREMENT_OFFSET 0.990476
#define VOLTAGE_DIVIDER_RATIO 3.0
#define NUM_SAMPLES 10  // Adjust for more/less smoothing

static float voltage_samples[NUM_SAMPLES] = { 0 };
static int sample_index = 0;
static int samples_filled = 0;   // how many slots hold a REAL reading (audit FB8)
esp_adc_cal_characteristics_t adc_chars;

float BAT_analogVolts = 0;

// One instantaneous, unsmoothed reading.
static float bat_read_raw_volts()
{
    int raw = analogRead(BAT_ADC_PIN);
    uint32_t voltage_mv = esp_adc_cal_raw_to_voltage(raw, &adc_chars);
    return (voltage_mv * VOLTAGE_DIVIDER_RATIO / 1000.0) / MEASUREMENT_OFFSET;
}

void BAT_Init()
{
    analogReadResolution(12);  // 12-bit ADC (0-4095)
    esp_adc_cal_characterize(ADC_UNIT_1, ADC_ATTEN_DB_11, ADC_WIDTH_BIT_12, DEFAULT_VREF, &adc_chars);

    // Audit FB8: PRIME the smoothing ring. It is zero-initialised and BAT_Get_Volts() used to
    // divide by the full NUM_SAMPLES from the very first call, so the average was diluted by 9
    // zeros -- roughly a tenth of the true voltage, i.e. below the 3.25 V floor of
    // BAT_Get_Percentage's table, which returns 0. The first caller is the boot POST line
    // ("BATTERY: %d%%"), so EVERY badge told its buyer the battery was dead on the very first
    // frame, and the 2 s status bar then read "BAT 0%" for the next ~10 ticks. It also made the
    // POST battery line useless as a production QC check on a 152-badge run.
    float v = bat_read_raw_volts();
    for (int i = 0; i < NUM_SAMPLES; i++) voltage_samples[i] = v;
    samples_filled = NUM_SAMPLES;
    sample_index = 0;
    BAT_analogVolts = v;
}

float BAT_Get_Volts()
{
    // Store the new voltage sample
    voltage_samples[sample_index] = bat_read_raw_volts();
    sample_index = (sample_index + 1) % NUM_SAMPLES;  // Circular buffer index
    if (samples_filled < NUM_SAMPLES) samples_filled++;

    // Average over the slots that actually hold a reading. Belt-and-braces with the priming
    // above: this stays correct even if a caller reaches BAT_Get_Volts() before BAT_Init().
    float sum = 0;
    for (int i = 0; i < samples_filled; i++)
    {
        sum += voltage_samples[i];
    }
    BAT_analogVolts = (samples_filled > 0) ? (sum / samples_filled) : 0.0f;

    return BAT_analogVolts;
}


int BAT_Get_Percentage(float voltage)
{
    static const struct
    {
        int percent;
        float voltage;
    } battery_table[] = {
        {100, 4.15}, {90, 4.06}, {80, 3.97}, {70, 3.88},
        {60, 3.79}, {50, 3.7}, {40, 3.61}, {30, 3.52},
        {20, 3.43}, {10, 3.34}, {0, 3.25}
    };

    for (size_t i = 0; i < sizeof(battery_table) / sizeof(battery_table[0]); i++)
    {
        if (voltage >= battery_table[i].voltage)
        {
            return battery_table[i].percent;
        }
    }
    return 0;  // Default to 0% if below the lowest threshold
}
