SafeHazard/Clip-Boy/Clip-Boy/nuclear_60x60.c

#include <lvgl.h>

#ifndef LV_ATTRIBUTE_NUCLEAR_60X60
#define LV_ATTRIBUTE_NUCLEAR_60X60
#endif

static const
LV_ATTRIBUTE_MEM_ALIGN LV_ATTRIBUTE_LARGE_CONST LV_ATTRIBUTE_NUCLEAR_60X60
uint8_t nuclear_60x60_map[] = {
    0x00,0x00,0x00,0x00,0x00,0x00,0x00,0x00,0x00,0x00,0x00,0x00,0x00,0x00,0x00,0x00,
    0x00,0x00,0x00,0x00,0x00,0x00,0x00,0x02,0x03,0x00,0x00,0x00,0x00,0x00,0x00,0x00,
    0x00,0x00,0x00,0x03,0x02,0x00,0x00,0x00,0x00,0x00,0x00,0x00,0x00,0x00,0x00,0x00,
    0x00,0x00,0x00,0x00,0x00,0x00,0x00,0x00,0x00,0x00,0x00,0x00,0x00,0x00,0x00,0x00,
    0x00,0x00,0x00,0x00,0x00,0x00,0x00,0x00,0x00,0x00,0x00,0x00,0x00,0x00,0x00,0x02,
    0x03,0x00,0x00,0x00,0x00,0x04,0x2c,0x40,0x4c,0x4e,0x4f,0x4d,0x42,0x2e,0x06,0x00,
    0x00,0x00,0x00,0x03,0x02,0x00,0x00,0x00,0x00,0x00,0x00,0x00,0x00,0x00,0x00,0x00,
    0x00,0x00,0x00,0x00,0x00,0x00,0x00,0x00,0x00,0x00,0x00,0x00,0x00,0x00,0x00,0x00,
    0x00,0x00,0x00,0x00,0x00,0x00,0x00,0x00,0x00,0x02,0x02,0x00,0x00,0x01,0x15,0x46,
    0x6e,0x95,0xc8,0xc9,0xc9,0xc9,0xc8,0xc9,0xc9,0xc8,0x99,0x72,0x4a,0x18,0x02,0x00,
    0x00,0x02,0x02,0x00,0x00,0x00,0x00,0x00,0x00,0x00,0x00,0x00,0x00,0x00,0x00,0x00,
    0x00,0x00,0x00,0x00,0x00,0x00,0x00,0x00,0x00,0x00,0x00,0x00,0x00,0x00,0x00,0x00,
    0x00,0x00,0x00,0x01,0x02,0x00,0x00,0x1c,0x53,0x95,0xc2,0xc8,0xce,0xc5,0xac,0x8e,
    0x76,0x6a,0x64,0x73,0x8f,0xa9,0xc3,0xcd,0xc9,0xc3,0x9a,0x57,0x22,0x00,0x00,0x01,
    0x01,0x00,0x00,0x00,0x00,0x00,0x00,0x00,0x00,0x00,0x00,0x00,0x00,0x00,0x00,0x00,
    0x00,0x00,0x00,0x00,0x00,0x00,0x00,0x00,0x00,0x00,0x00,0x00,0x00,0x00,0x02,0x00,
    0x00,0x21,0x77,0xb8,0xd0,0xc5,0x9d,0x72,0x3c,0x21,0x17,0x09,0x02,0x00,0x00,0x01,
    0x09,0x17,0x20,0x38,0x6f,0x9a,0xc2,0xd1,0xbd,0x7b,0x27,0x00,0x00,0x02,0x01,0x00,
    0x00,0x00,0x00,0x00,0x00,0x00,0x00,0x00,0x00,0x00,0x00,0x00,0x00,0x00,0x00,0x00,
    0x00,0x00,0x00,0x00,0x00,0x00,0x00,0x00,0x01,0x01,0x00,0x15,0x73,0xc1,0xcd,0xb1,
    0x63,0x33,0x02,0x00,0x00,0x00,0x00,0x00,0x03,0x05,0x05,0x03,0x00,0x00,0x00,0x00,
    0x00,0x00,0x30,0x5a,0xa9,0xcc,0xc4,0x7c,0x1e,0x00,0x00,0x02,0x00,0x00,0x00,0x00,
    0x00,0x00,0x00,0x00,0x00,0x00,0x00,0x00,0x00,0x00,0x00,0x00,0x00,0x00,0x00,0x00,
    0x00,0x00,0x00,0x02,0x00,0x00,0x55,0xb6,0xcf,0xa9,0x5c,0x0e,0x00,0x00,0x00,0x10,
    0x37,0x59,0x74,0x89,0x9e,0xa3,0xa3,0x9f,0x8c,0x77,0x5d,0x3a,0x16,0x00,0x00,0x00,
    0x09,0x53,0xa1,0xcd,0xbf,0x5d,0x06,0x00,0x02,0x00,0x00,0x00,0x00,0x00,0x00,0x00,
    0x00,0x00,0x00,0x00,0x00,0x00,0x00,0x00,0x00,0x00,0x00,0x00,0x00,0x00,0x02,0x00,
    0x16,0x86,0xca,0xbc,0x5e,0x12,0x00,0x00,0x0d,0x3e,0x81,0xaa,0xc1,0xc8,0xc8,0xc6,
    0xc4,0xc4,0xc4,0xc4,0xc6,0xc8,0xc8,0xc2,0xad,0x85,0x45,0x11,0x00,0x00,0x0d,0x5c,
    0xb3,0xcc,0x95,0x1c,0x00,0x02,0x00,0x00,0x00,0x00,0x00,0x00,0x00,0x00,0x00,0x00,
    0x00,0x00,0x00,0x00,0x00,0x00,0x00,0x00,0x00,0x03,0x00,0x27,0xa6,0xcf,0x98,0x25,
    0x00,0x00,0x0a,0x56,0xa2,0xc5,0xc6,0xc4,0xc0,0xbd,0xbd,0xbe,0xbf,0xbf,0xbf,0xbf,
    0xbe,0xbd,0xbd,0xbf,0xc3,0xc6,0xc7,0xa7,0x5d,0x10,0x00,0x00,0x1b,0x8c,0xce,0xab,
    0x30,0x00,0x03,0x00,0x00,0x00,0x00,0x00,0x00,0x00,0x00,0x00,0x00,0x00,0x00,0x00,
    0x00,0x00,0x00,0x00,0x03,0x00,0x31,0xb3,0xcd,0x72,0x08,0x00,0x00,0x41,0x9f,0xc6,
    0xc4,0xbe,0xbe,0xbf,0xbf,0xc0,0xc0,0xc0,0xc0,0xc0,0xc0,0xc0,0xc0,0xc0,0xc0,0xc0,
    0xbf,0xbe,0xbe,0xc4,0xc6,0xa5,0x4d,0x00,0x00,0x01,0x6b,0xcb,0xbc,0x3e,0x00,0x04,
    0x00,0x00,0x00,0x00,0x00,0x00,0x00,0x00,0x00,0x00,0x00,0x00,0x00,0x00,0x00,0x02,
    0x00,0x34,0xb9,0xc6,0x5b,0x00,0x00,0x11,0x78,0xc4,0xca,0xc2,0xbd,0xc0,0xc0,0xc0,
    0xc0,0xc0,0xc0,0xc0,0xc0,0xc0,0xc0,0xc0,0xc0,0xc0,0xc0,0xc0,0xc0,0xc0,0xc0,0xbe,
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
};

const lv_image_dsc_t nuclear_60x60 = {
  .header = {
    .magic = LV_IMAGE_HEADER_MAGIC,
    .cf = LV_COLOR_FORMAT_A8,
    .flags = 0,
    .w = 60,
    .h = 60,
    .stride = 60,
    .reserved_2 = 0,
  },
  .data_size = sizeof(nuclear_60x60_map),
  .data = nuclear_60x60_map,
  .reserved = NULL,
};
