SafeHazard/Clip-Boy/Clip-Boy/rift_private.h

#pragma once
// VANILLA rift colorways (PUBLIC edition). The real Overseer/Space Badge palettes
// are KS-backer-exclusive and NOT in the public source; these generic placeholders
// keep the --rift theme slots valid. Format matches the consuming sites in
// ui_theme.h / ui_nav.h. (See the gate in ui_theme.h.)
#define RIFT_THEME_OVERSEER \
    "Rift Blue", 0x05080F, 0x4A90D8, 0x7AB4E8, 0x2A4870, 0x4A90D8, 0x03060C, 0x244468, 0x40506A, true
#define RIFT_THEME_SPACE_BADGE \
    "Rift Red", 0x0C0000, 0xD85448, 0xE87868, 0x603434, 0xD85448, 0x0C0606, 0x603434, 0x50403A, true
#define RIFT_LED_OV_R  40,120,200, 80,160,240,120,200
#define RIFT_LED_OV_G  80,140,200, 80,140,200, 80,140
#define RIFT_LED_OV_B 200,240,255,200,240,255,200,240
#define RIFT_LED_SB_R 200, 80,160,240,120,200, 80,160
#define RIFT_LED_SB_G  60,100,140, 60,100,140, 60,100
#define RIFT_LED_SB_B  80,120,180, 80,120,180, 80,120
